NilujePerchut/doppelganger_hardware/arcade_adapter/Documentation interne/Supergun MAK Strike - ArcadeForge_fichiers/74_0.jpg

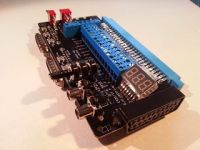
arcade_adapter/Documentation interne/Supergun MAK Strike - ArcadeForge_fichiers/74_0.jpg
