NilujePerchut/doppelganger_hardware/arcade_adapter/Documentation interne/Supergun MAK Strike - ArcadeForge_fichiers/MAK_010.JPG

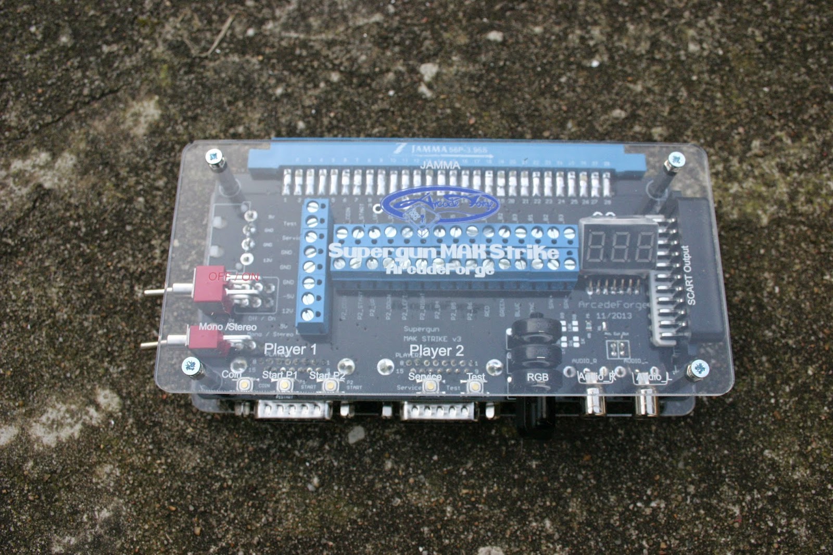
arcade_adapter/Documentation interne/Supergun MAK Strike - ArcadeForge_fichiers/MAK_010.JPG
