NilujePerchut/doppelganger_hardware/arcade_adapter/Documentation interne/Supergun MAK Strike - ArcadeForge_fichiers/MAK_Strike_v3_05.jpg

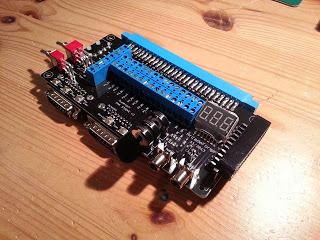
arcade_adapter/Documentation interne/Supergun MAK Strike - ArcadeForge_fichiers/MAK_Strike_v3_05.jpg
