NilujePerchut/doppelganger_hardware/main_board/Documentation_Interne/fb.jpg

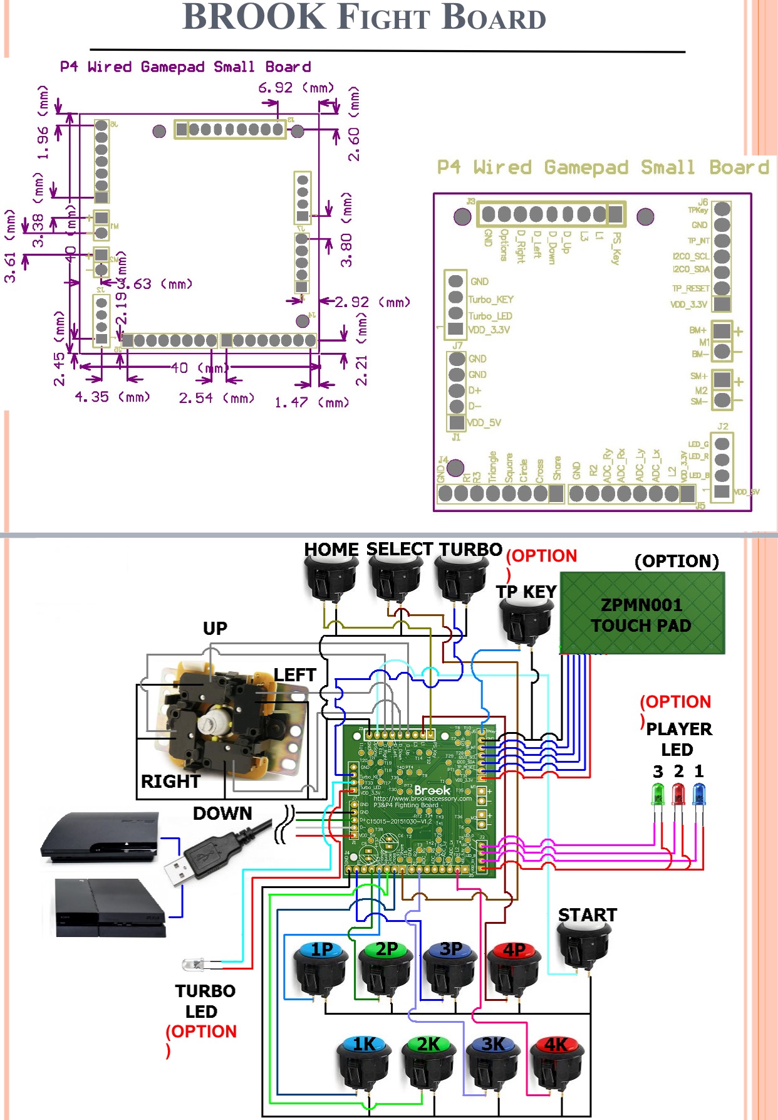
main_board/Documentation_Interne/fb.jpg
