NilujePerchut/doppelganger_hardware/main_board/Documentation_Interne/ps3ps4-fighting-board.jpg

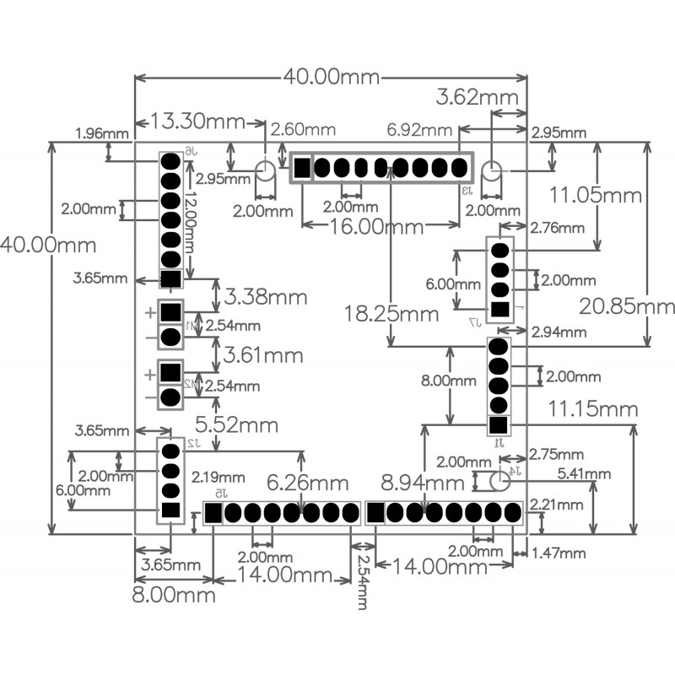
main_board/Documentation_Interne/ps3ps4-fighting-board.jpg
