NilujePerchut/doppelganger_hardware/main_board/Documentation_Interne/New/RJ45(1860580).pdf

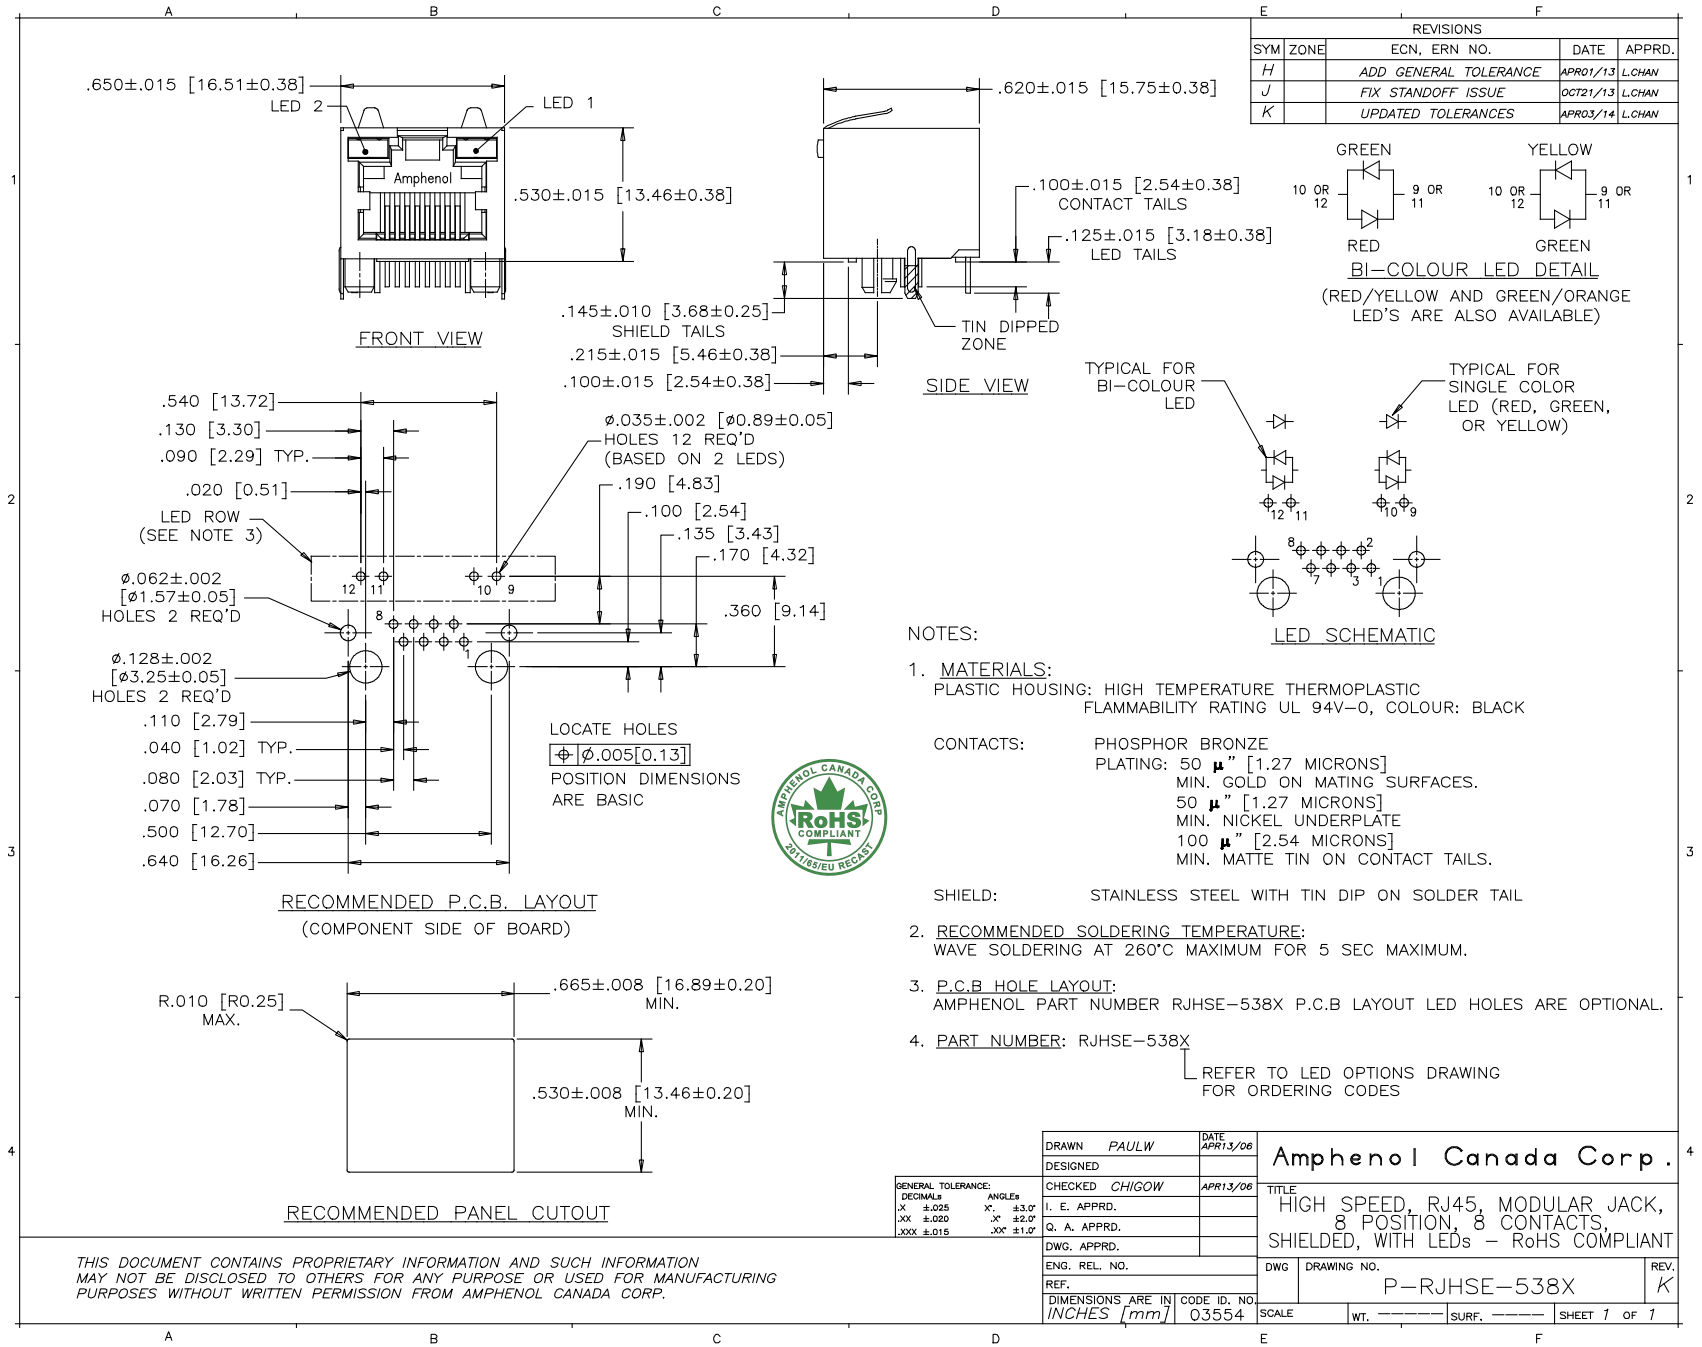
[picture p22: page 1]

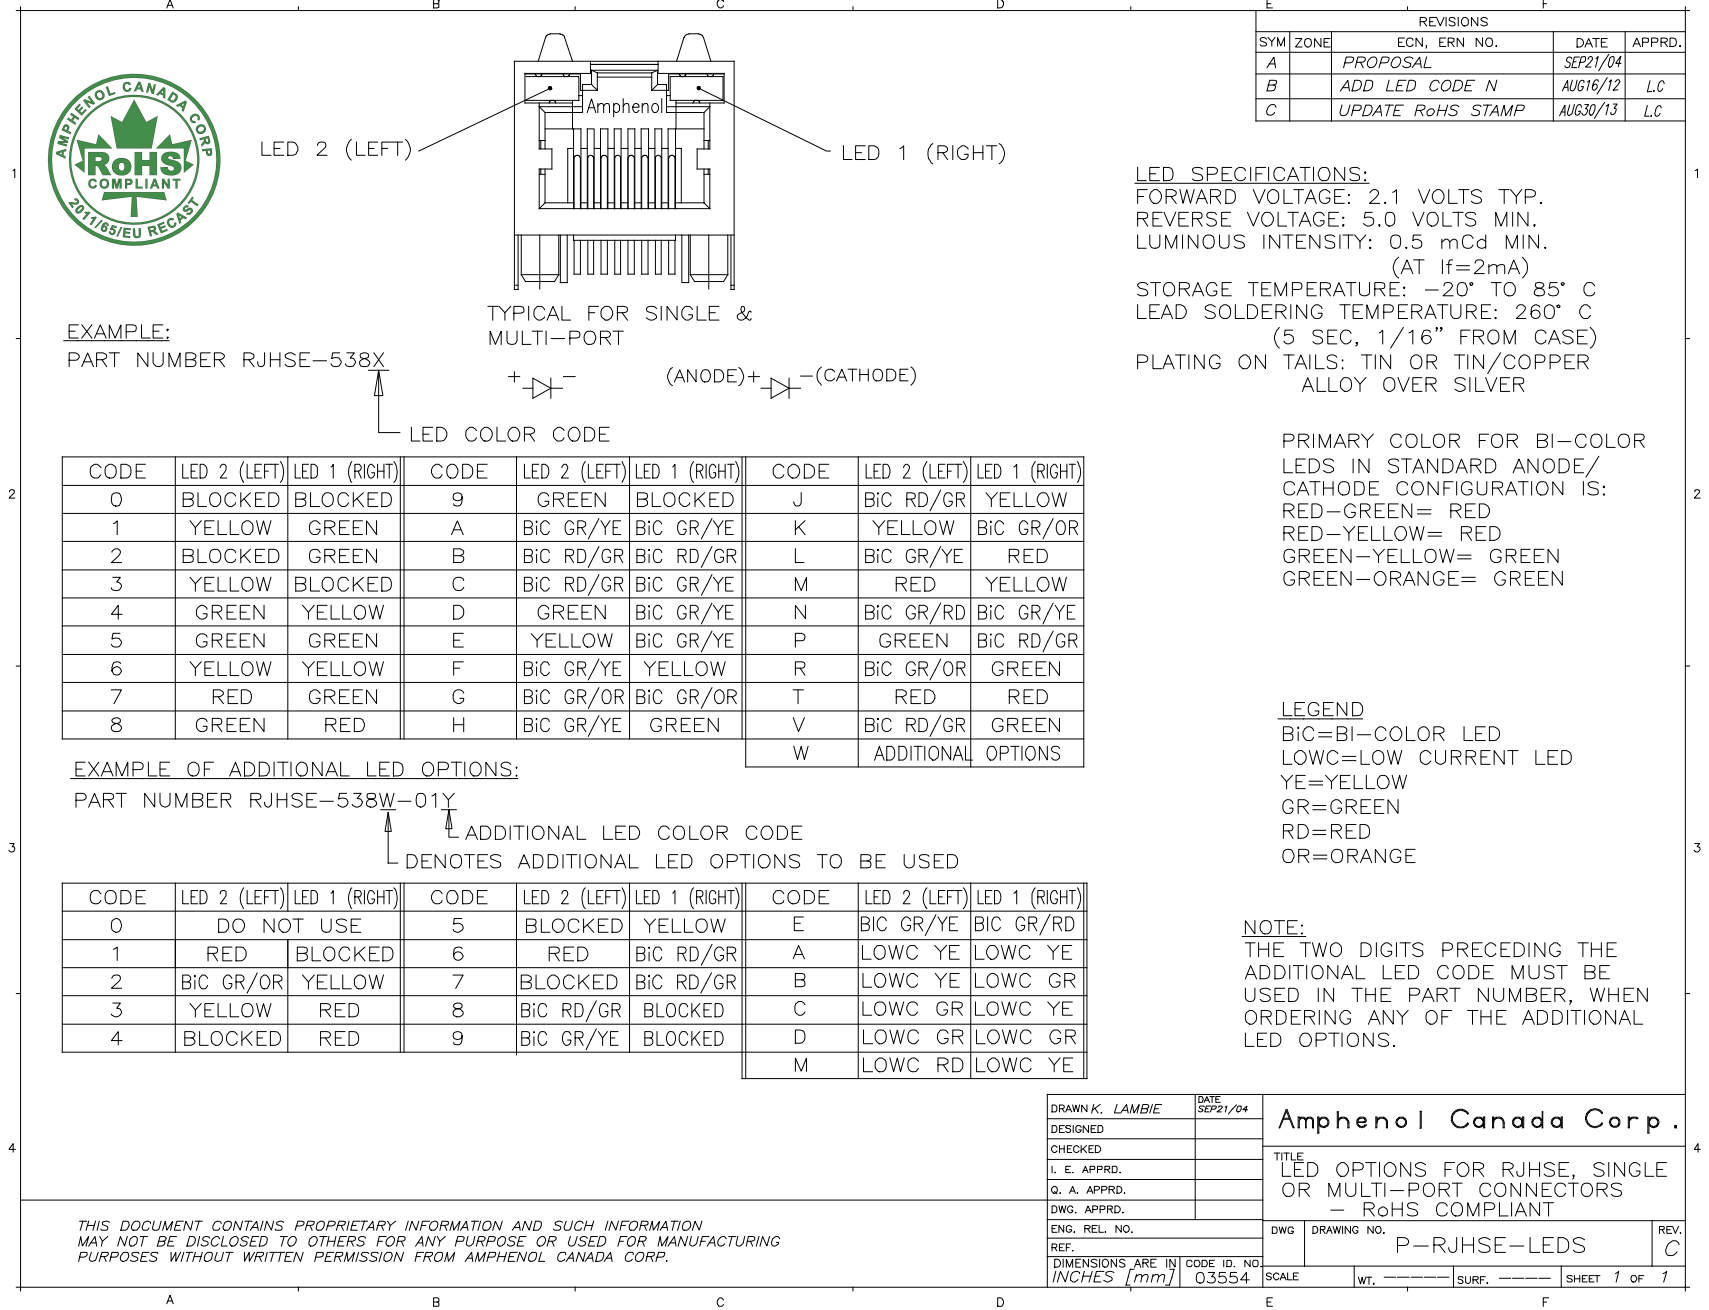
[picture p23: page 2]
